Peppson/Radio-Nodes/Code/Node 11 Mocca_master/include/info.h

/*
#######################  Attiny84A Pinout  #########################
#                                                                  #
#                        VCC  1|o   |14 GND                        #
#  (Tiny_serial out) --- PB0  2|    |13 A0/0 --- ADC_MEASURE_PIN   #
#          SERVO_PIN --- PB1  3|    |12 A1/1 ---                   #
#      Pullup R 100K --- RST  4|    |11 A2/2 --- RF24 CE           #
#                    --- PB2  5|    |10 A3/3 --- RF24 CSN          #
#                   --- A7/7  6|    |9  A4/4 --- RF24 SCK          #
#         RF24 MISO --- A6/6  7|    |8  A5/5 --- RF24 MOSI         #
#                                                                  #
####################################################################


######################  RF24 message package  ######################
#                                                                  #
# - ATtiny84A have 2 bytes for Tx and Rx buffers...                #
# - splitting up package into small chunks of data                 #
#                                                                  #
# - uint16_t RF24_package[6] = {}                                  #
# - RF24_package[0] = from_who                                     #
# - RF24_package[1] = to_who                                       #
# - RF24_package[2] = data 0                                       #
# - RF24_package[3] = data 1                                       #
# - RF24_package[4] = bool                                         #
# - RF24_package[5] = time                                         #
#                                                                  #
####################################################################


Servo postitons:
On = 550
On_middle = 800
Off = 1300
Off_middle = 950


*/
